MColombari/SmartBottle/Arduino_Bottle/Tests/Bluetooth_Test/Bluetooth_Test/Bluetooth_Test.ino

#include <SoftwareSerial.h>


#define softrx 2    // Connect to TX of HC-05.
#define softtx 3    // Connect to RX of HC-05.
SoftwareSerial BTSerial(softrx, softtx); // RX | TX

int count;

void setup() {
  
  pinMode(softrx, INPUT);
  pinMode(softtx, OUTPUT);
  
  BTSerial.begin(9600);
  Serial.begin(9600);
}

void loop() {
  if (BTSerial.available())
  {
    Serial.write(BTSerial.read());
  }
  if (Serial.available())
  {
    BTSerial.write(Serial.read());
  }
}
